telzo2000/cool650lp/img/img00003.jpg

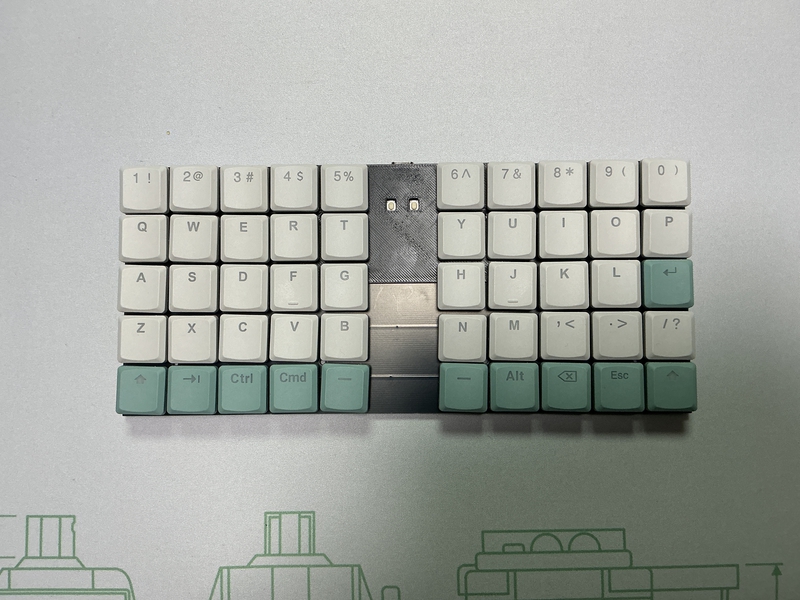
img/img00003.jpg
